lmolteno/eq_driver/firmware/esp/main/hello_world_main.c

#include <stdio.h>
#include <inttypes.h>
#include "sdkconfig.h"
#include "freertos/FreeRTOS.h"
#include "freertos/task.h"
#include "esp_chip_info.h"
#include "esp_flash.h"
#include "esp_system.h"
#include "esp_log.h"
#include "telescope_protocol.h"
#include "bluetooth_control.h"

static const char *TAG = "main";

void app_main(void)
{
    printf("ESP32 Telescope Controller Starting...\n");

    /* Print chip information */
    esp_chip_info_t chip_info;
    uint32_t flash_size;
    esp_chip_info(&chip_info);
    printf("This is %s chip with %d CPU core(s), %s%s%s%s, ",
           CONFIG_IDF_TARGET,
           chip_info.cores,
           (chip_info.features & CHIP_FEATURE_WIFI_BGN) ? "WiFi/" : "",
           (chip_info.features & CHIP_FEATURE_BT) ? "BT" : "",
           (chip_info.features & CHIP_FEATURE_BLE) ? "BLE" : "",
           (chip_info.features & CHIP_FEATURE_IEEE802154) ? ", 802.15.4 (Zigbee/Thread)" : "");

    unsigned major_rev = chip_info.revision / 100;
    unsigned minor_rev = chip_info.revision % 100;
    printf("silicon revision v%d.%d, ", major_rev, minor_rev);
    if(esp_flash_get_size(NULL, &flash_size) != ESP_OK) {
        printf("Get flash size failed");
        return;
    }

    printf("%" PRIu32 "MB %s flash\n", flash_size / (uint32_t)(1024 * 1024),
           (chip_info.features & CHIP_FEATURE_EMB_FLASH) ? "embedded" : "external");

    printf("Minimum free heap size: %" PRIu32 " bytes\n", esp_get_minimum_free_heap_size());

    // Initialize telescope protocol
    esp_err_t ret = protocol_init();
    if (ret != ESP_OK) {
        ESP_LOGE(TAG, "Failed to initialize telescope protocol: %s", esp_err_to_name(ret));
        return;
    }

    // Initialize Bluetooth control
    ret = bluetooth_control_init();
    if (ret != ESP_OK) {
        ESP_LOGE(TAG, "Failed to initialize Bluetooth control: %s", esp_err_to_name(ret));
        return;
    }

    ESP_LOGI(TAG, "ESP32 Telescope Controller initialized successfully");
    printf("\n=== ESP32 Telescope Controller Ready ===\n");
    printf("UART Communication: RX=IO0, TX=IO45\n");
    printf("Bluetooth Device: %s\n", "Telescope_Controller");
    printf("Automatically requesting status from RP2040 every 5 seconds\n");
    printf("Status updates will be displayed below:\n");
    printf("Bluetooth commands: SET_RA_GEAR, SET_DEC_GEAR, JOG_RA_POS/NEG, JOG_DEC_POS/NEG, SYNC, STATUS\n\n");

    // Main application continues to run while protocol task handles communication
    while (1) {
        vTaskDelay(pdMS_TO_TICKS(10000)); // 10 second delay between heartbeat messages
        ESP_LOGI(TAG, "ESP32 main loop running, free heap: %" PRIu32 " bytes", esp_get_free_heap_size());
    }
}
